gardner-lab/FinchScope/ActiveComm/img/hall_sensor _latch.png

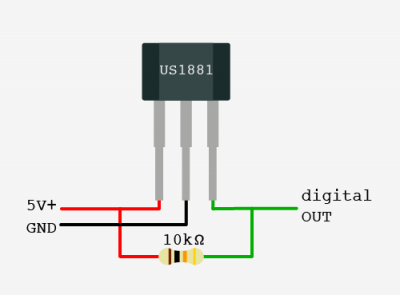
ActiveComm/img/hall_sensor _latch.png
