gardner-lab/FinchScope/ActiveComm/img/IMG_0866.JPG

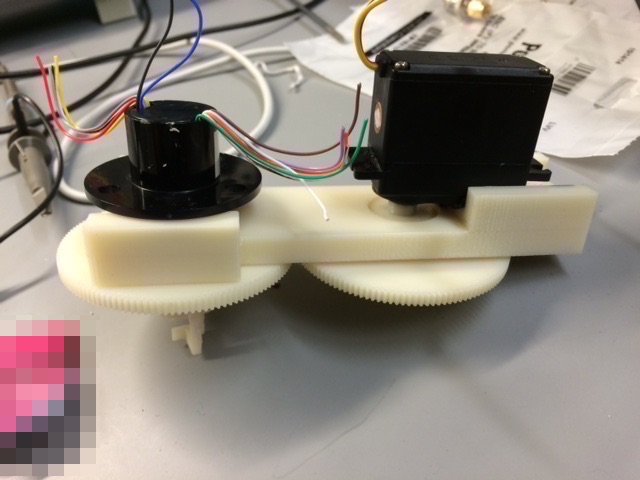
ActiveComm/img/IMG_0866.JPG
