gardner-lab/FinchScope/ActiveComm/img/IMG_1855.JPG

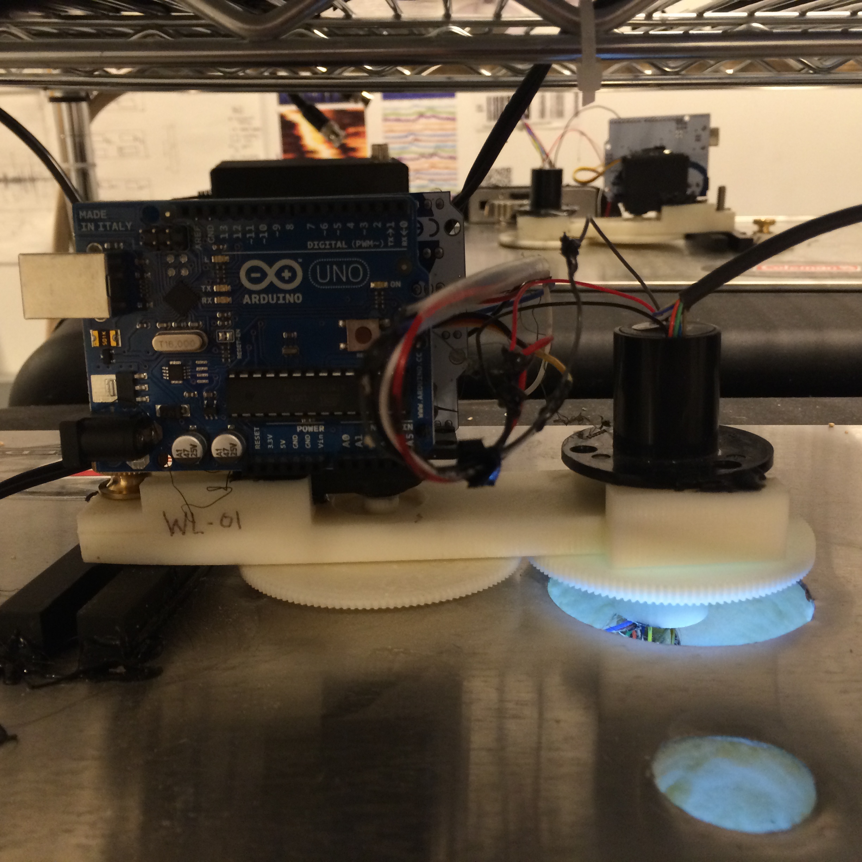
ActiveComm/img/IMG_1855.JPG
