gardner-lab/FinchScope/ActiveComm/img/IMG_1856.JPG

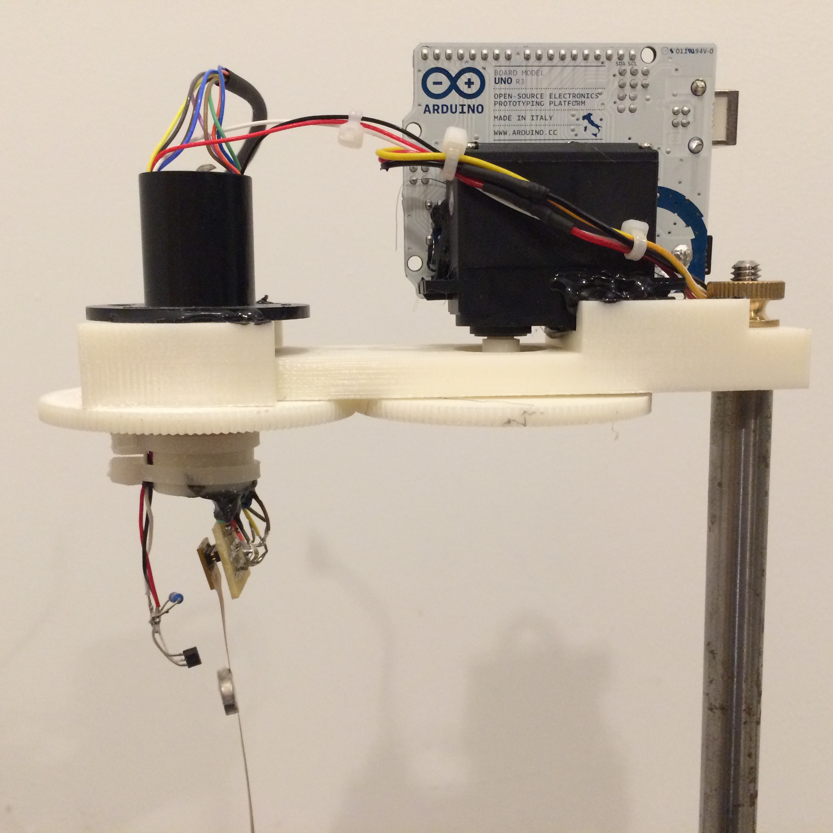
ActiveComm/img/IMG_1856.JPG
