gardner-lab/FinchScope/ActiveComm/img/IMG_1862.JPG

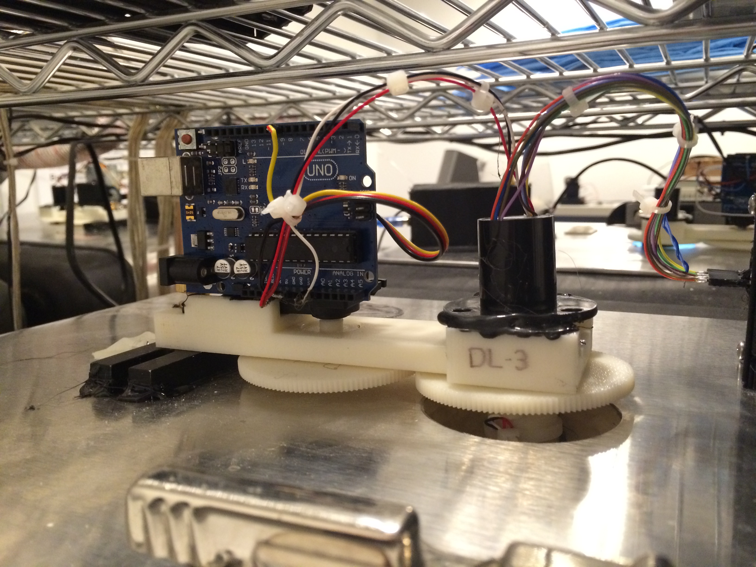
ActiveComm/img/IMG_1862.JPG
