gardner-lab/FinchScope/Analysis Pipeline/EXAMPLE_DFF2.png

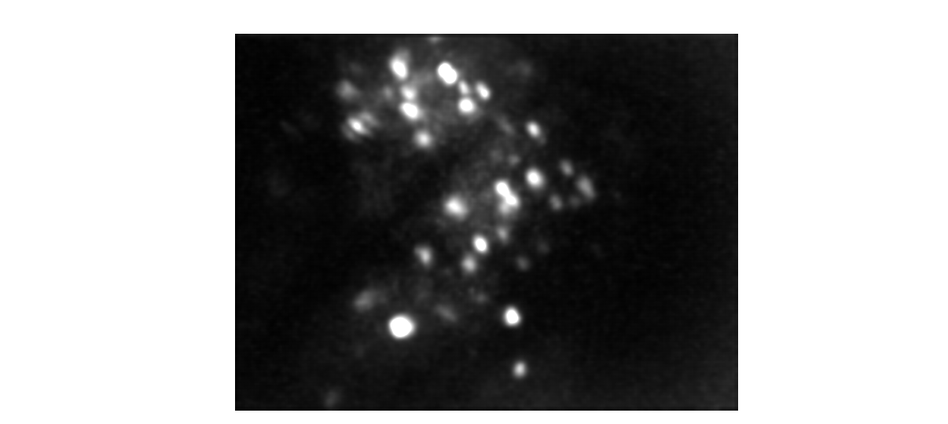
Analysis Pipeline/EXAMPLE_DFF2.png
