gardner-lab/FinchScope/Analysis Pipeline/EXAMPLE_DFF.png

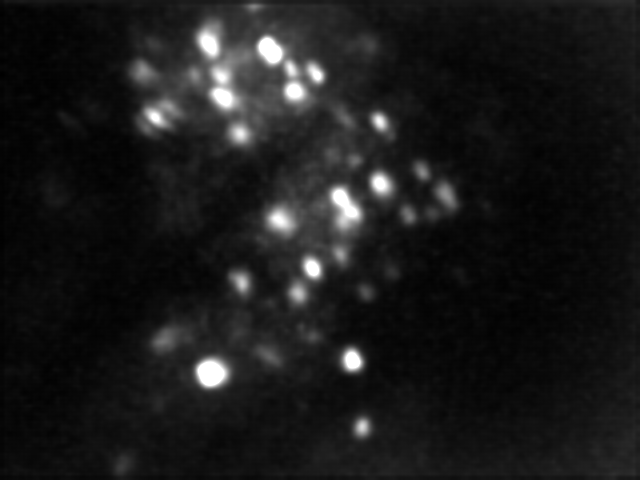
Analysis Pipeline/EXAMPLE_DFF.png
