gardner-lab/FinchScope/Analysis Pipeline/ROI_MAP.png

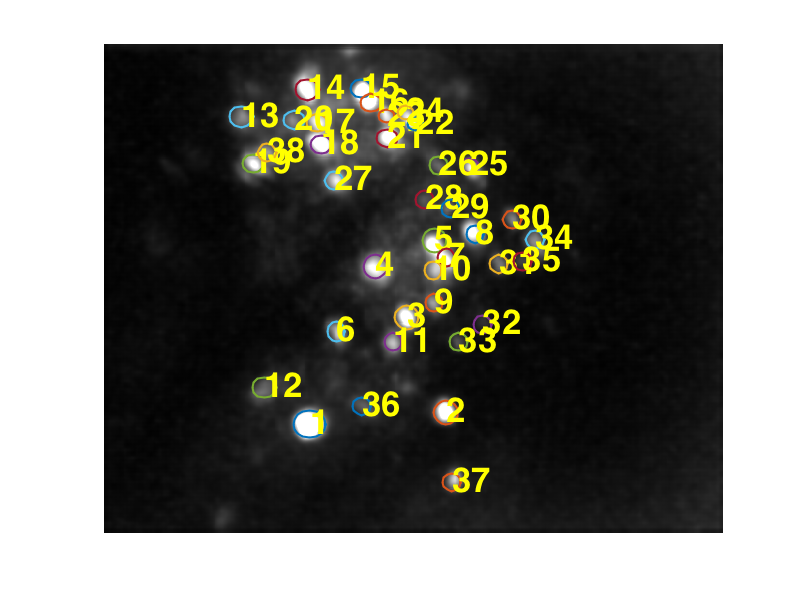
Analysis Pipeline/ROI_MAP.png
