gardner-lab/FinchScope/Analysis Pipeline/SW_im1.png

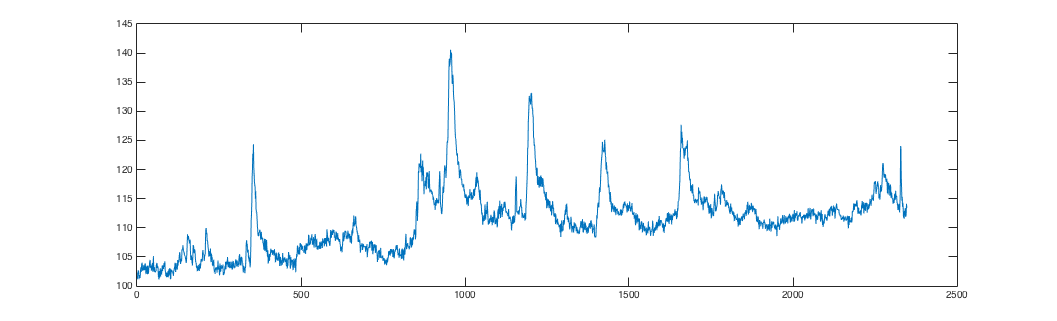
Analysis Pipeline/SW_im1.png
