gardner-lab/FinchScope/Analysis Pipeline/SW_im2.png

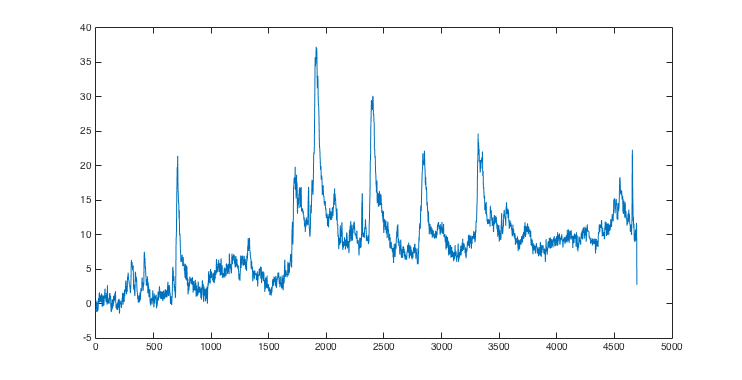
Analysis Pipeline/SW_im2.png
