gardner-lab/FinchScope/Analysis Pipeline/SW_im3.png

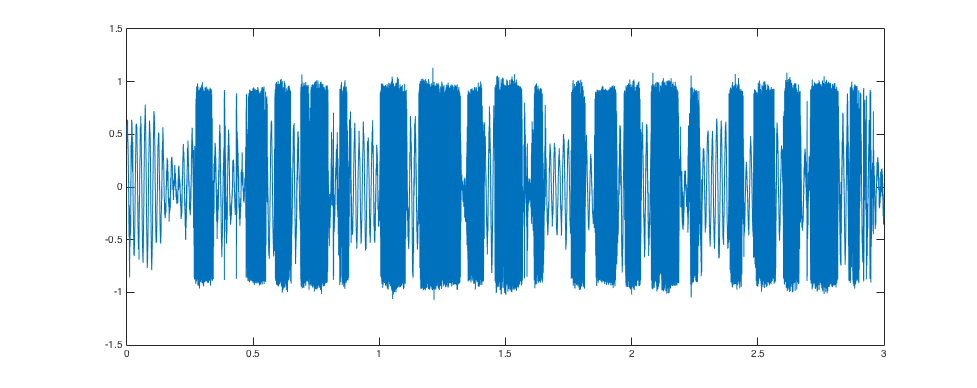
Analysis Pipeline/SW_im3.png
