gardner-lab/FinchScope/FinchScope/FlexCables/Screen Shot 2015-04-15 at 5.46.42 PM (1).png

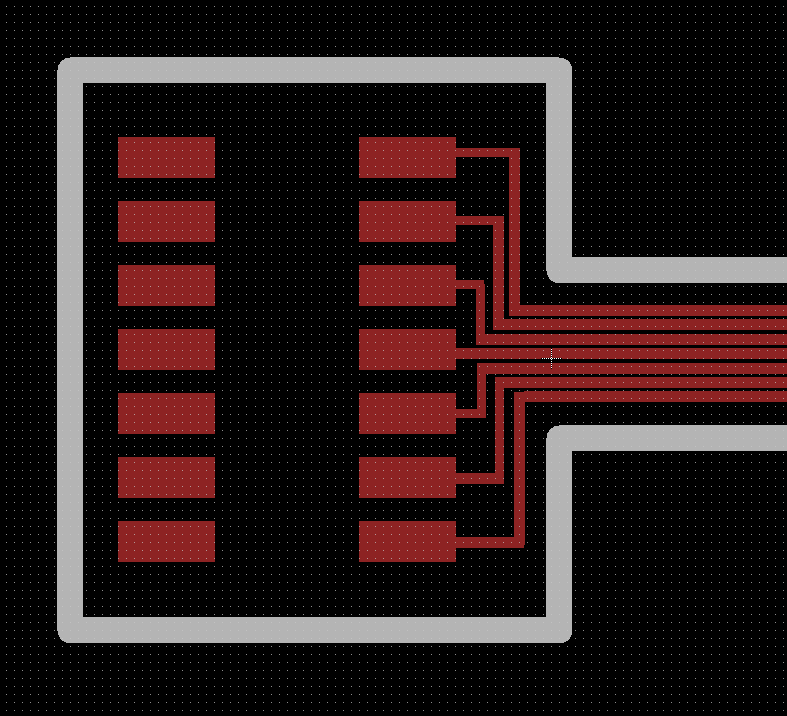
FinchScope/FlexCables/Screen Shot 2015-04-15 at 5.46.42 PM (1).png
