gardner-lab/FinchScope/FinchScope/img/ACS3_3a.png

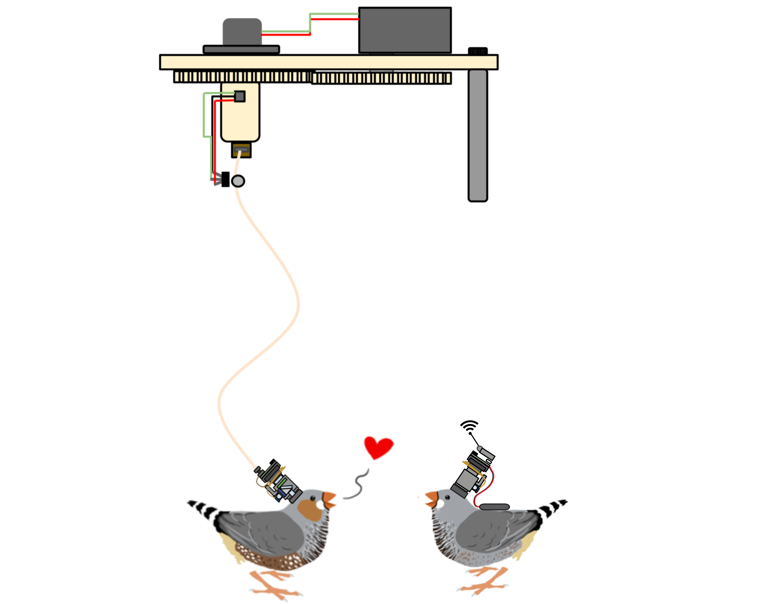
FinchScope/img/ACS3_3a.png
