gardner-lab/FinchScope/FinchScope/DesignFiles/FinchScope/BaseplateMk1.3.stl

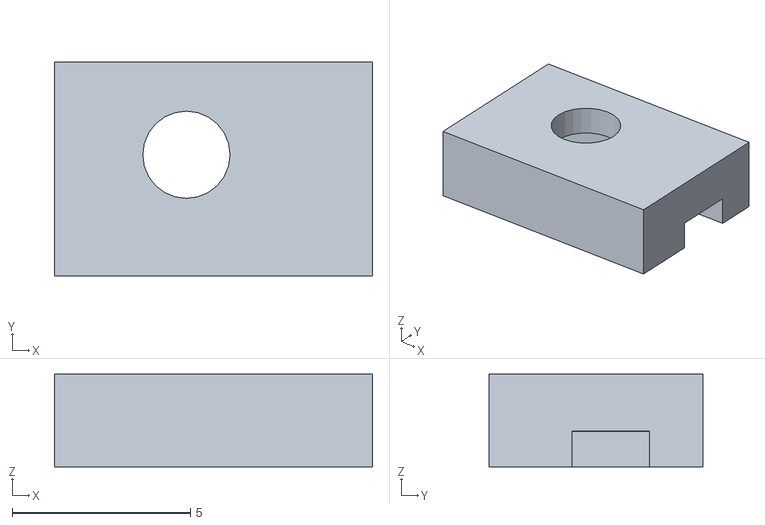
[picture p45: CAD file, 2016-03-16]
FinchScope/DesignFiles/FinchScope/BaseplateMk1.3.stl
8.92 x 6.00 x 2.60
