gardner-lab/FinchScope/Activecom/DesignFiles/ActiveCommutator/ActiveCommGear2.stl

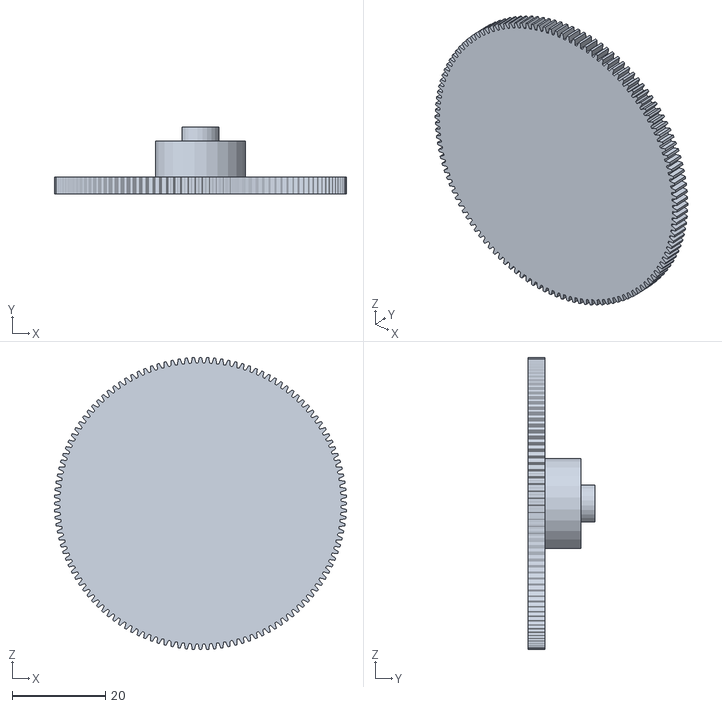
[picture p46: CAD file, 2015-01-10]
Activecom/DesignFiles/ActiveCommutator/ActiveCommGear2.stl
62.8 x 14.3 x 62.8
