gardner-lab/FinchScope/FinchScope/DesignFiles/CaBMI_miniscope/miniTo2P.stl

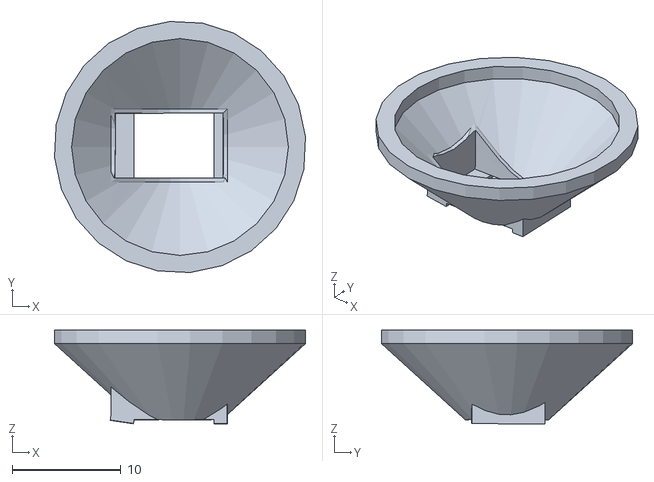
[picture p47: CAD file, 2019-08-05]
FinchScope/DesignFiles/CaBMI_miniscope/miniTo2P.stl
23.1 x 23.1 x 8.62
