gardner-lab/FinchScope/FinchScope/DesignFiles/FinchScope/FinchScopeMk5.4.stl

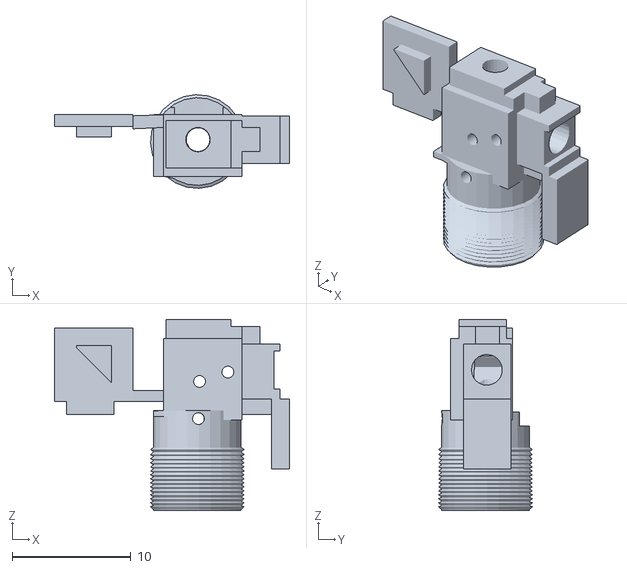
[picture p48: CAD file, 2015-04-23]
FinchScope/DesignFiles/FinchScope/FinchScopeMk5.4.stl
19.8 x 7.90 x 16.1
