gardner-lab/FinchScope/FinchScope/DesignFiles/FinchScope/FinchScopeCapMk1.0.stl

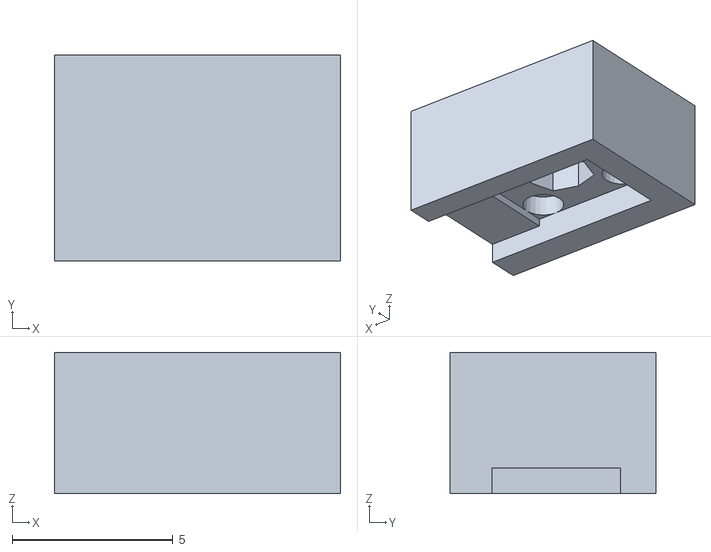
[picture p49: CAD file, 2014-12-26]
FinchScope/DesignFiles/FinchScope/FinchScopeCapMk1.0.stl
8.90 x 6.40 x 4.40
