gardner-lab/FinchScope/FinchScope/DesignFiles/CaBMI_miniscope/CaBMI_miniscope_Short_stem_1.8.stl

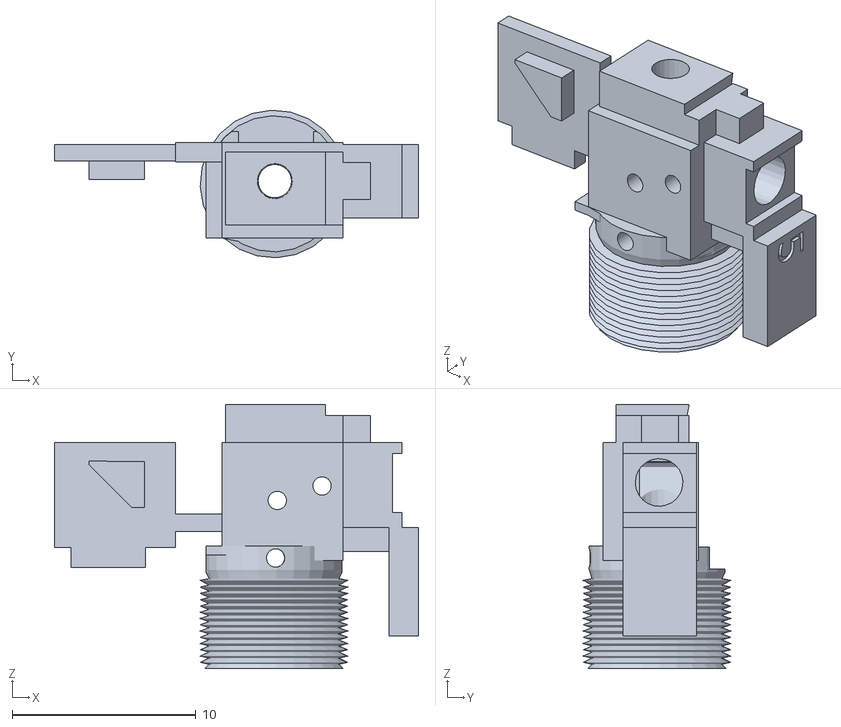
[picture p50: CAD file, 2019-08-05]
FinchScope/DesignFiles/CaBMI_miniscope/CaBMI_miniscope_Short_stem_1.8.stl
19.8 x 8.03 x 14.4
