gardner-lab/FinchScope/FinchScope/DesignFiles/FinchScope/BaseplateCoverV1.stl

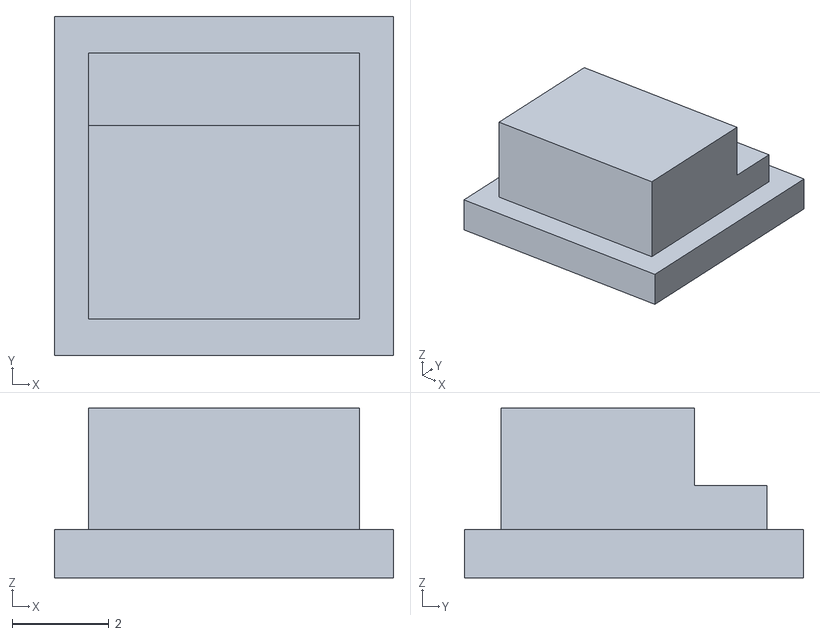
[picture p51: CAD file, 2014-12-25]
FinchScope/DesignFiles/FinchScope/BaseplateCoverV1.stl
7.00 x 7.00 x 3.50
