gardner-lab/FinchScope/FinchScope/DesignFiles/CaBMI_miniscope/CaBMI_miniscope.stl

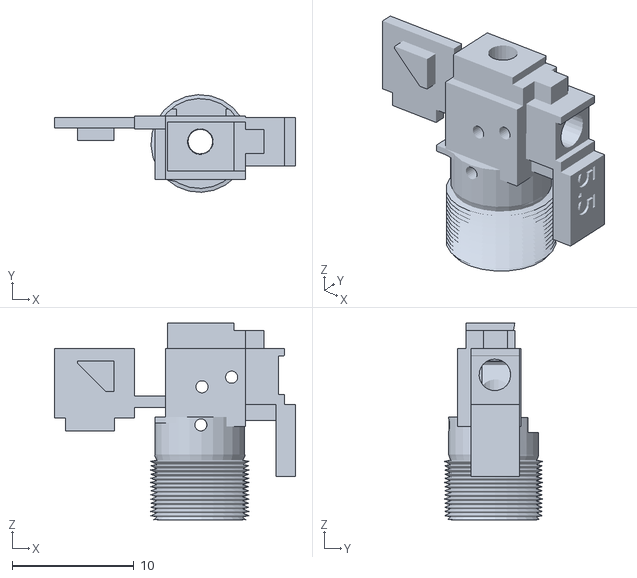
[picture p52: CAD file, 2019-02-11]
FinchScope/DesignFiles/CaBMI_miniscope/CaBMI_miniscope.stl
19.8 x 8.03 x 16.2
