gardner-lab/FinchScope/FinchScope/DesignFiles/FinchScope/DummyEndoscopeV1.stl

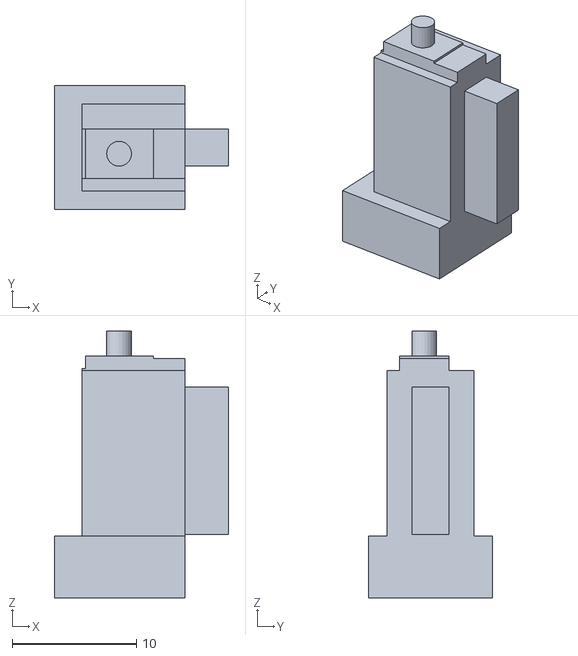
[picture p53: CAD file, 2014-12-25]
FinchScope/DesignFiles/FinchScope/DummyEndoscopeV1.stl
14.0 x 10.0 x 21.5
